gregsell/Paulmann-LED-driver/schematic/Paulmann_dimmable_led_spot_driver/Paulmann_dimmable_led_spot_driver.kicad_sch

## KiCad design schematic/Paulmann_dimmable_led_spot_driver/Paulmann_dimmable_led_spot_driver.kicad_sch (2026-10-07)

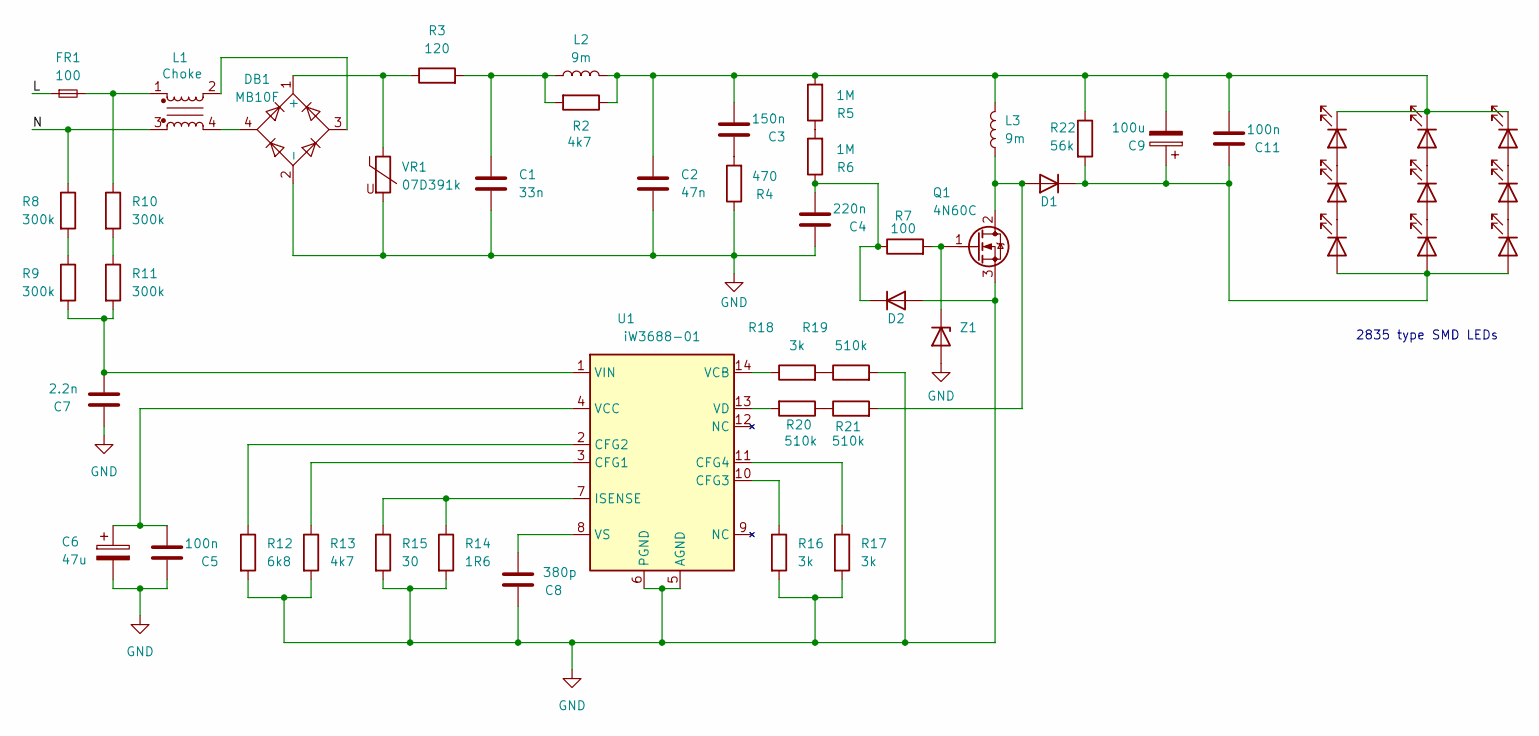
[picture p10: schematic Paulmann_dimmable_led_spot_driver.kicad_sch]

Parts:
C1: 33n
C2: 47n
C3: 150n
C4: 220n
C5, C11: 100n
C6: 47u
C7: 2.2n
C8: 380p
C9: 100u
D1, D2: 1N4001; D_DO-41_SOD81_P10.16mm_Horizontal
DB1: MB10F; TSSOP-4_4.4x5mm_P4mm
FR1: 100
L1: Choke; Choke_Schaffner_RN102-04-14.0x14.0mm
L2, L3: 9m
LED1, LED2, LED3, LED4, LED5, LED6, LED7, LED8, LED9: LED
Q1: 4N60C; SOT-223-3_TabPin2
R2, R13: 4k7
R3: 120
R4: 470
R5, R6: 1M
R7: 100
R8, R9, R10, R11: 300k
R12: 6k8
R14: 1R6
R15: 30
R16, R17, R18: 3k
R19, R20, R21: 510k
R22: 56k
U1: iW3688-01; SOIC-14
VR1: 07D391k
Z1: 19V

Connections:
GND: C1.2, C2.2, C4.1, C5.1, C6.2, C7.1, C8.1, D2.2 (A), DB1.2 (-), Q1.3 (S), R4.1, R12.2, R13.2, R14.2, R15.2, R16.2, R17.2, R19.2, U1.5 (AGND), U1.6 (PGND), U1.15 (PGND), VR1.2, Z1.2 (A)
L: FR1.1
N: L1.3, R8.1
unnamed: C1.1, L2.1, R2.2, R3.2
unnamed: C3.1, R4.2
unnamed: C4.2, D2.1 (K), R6.1, R7.1
unnamed: C5.2, C6.1, U1.4 (VCC)
unnamed: C7.2, R9.2, R11.2, U1.1 (VIN)
unnamed: C8.2, U1.8 (VS)
unnamed: C9.1, C11.1, D1.1 (K), LED3.2 (A), LED6.2 (A), LED9.2 (A), R22.2
unnamed: C2.1, C3.2, C9.2, C11.2, L2.2, L3.2, LED1.1 (K), LED4.1 (K), LED7.1 (K), R2.1, R5.2, R22.1
unnamed: D1.2 (A), L3.1, Q1.2 (D), R21.2
unnamed: DB1.1 (+), R3.1, VR1.1
unnamed: DB1.3, L1.2
unnamed: DB1.4, L1.4
unnamed: FR1.2, L1.1, R10.1
unnamed: LED1.2 (A), LED2.1 (K)
unnamed: LED2.2 (A), LED3.1 (K)
unnamed: LED4.2 (A), LED5.1 (K)
unnamed: LED5.2 (A), LED6.1 (K)
unnamed: LED7.2 (A), LED8.1 (K)
unnamed: LED8.2 (A), LED9.1 (K)
unnamed: Q1.1 (G), R7.2, Z1.1 (K)
unnamed: R5.1, R6.2
unnamed: R8.2, R9.1
unnamed: R10.2, R11.1
unnamed: R12.1, U1.2 (CFG2)
unnamed: R13.1, U1.3 (CFG1)
unnamed: R14.1, R15.1, U1.7 (ISENSE)
unnamed: R16.1, U1.10 (CFG3)
unnamed: R17.1, U1.11 (CFG4)
unnamed: R18.1, U1.14 (VCB)
unnamed: R18.2, R19.1
unnamed: R20.1, R21.1
unnamed: R20.2, U1.13 (VD)

Notes on the sheet:
2835 type SMD LEDs
